TDHolmes/BinaryClock/firmware/LED_drvr_STP16CPC26.c

#include "LED_drvr_STP16CPC26.h"
#include "LED.h"
#include "ports.h"
#include <stdint.h>

/*! \file LED_drvr_STP16CPC26.c
    \brief Low level LED driver functions to be used with the STP16CPC26 LED
    constant current driver.
*/

#define COLOR_DEPTH 4  //!< Number of bits of color to multiplex.


/*!
 * Initializes the LED driver structure and drives the anode port high to
 * avoid LEDs turning on.
 *
 * @param[in] LED_ptr (LED_drvr_t *): pointer to the LED driver structure.
 */
void LED_drvr_init(LED_drvr_t * LED_ptr)
{
    LED_ptr->active_column = 0;
    LED_ptr->active_color_bit = 0;
    ANO_PORT = 0xFF;
}


/*!
 * Runs the LED multiplexing code. Generates a bitstream to send to the LED
 * driver, then activates the corresponding column.
 *
 * @param[in] LED_ptr (LED_drvr_t *): pointer to the LED driver structure.
 */
void LED_drvr_run(LED_drvr_t *LED_ptr)
{
    uint16_t color_mask = (1 << LED_ptr->active_color_bit);
    uint16_t bitstream = 0;
    uint16_t bit = 0;
    uint8_t row;
    uint8_t i;

    // build up the bitstream to be clocked out
    for (row = 0; row < 4; row++) { // rows
        /*  --  RED  --   */
         // mask for color
        bit = (LED_ptr->LED_array[row][LED_ptr->active_column][RED_IND] & color_mask) >> LED_ptr->active_color_bit;
        // shift for bitstream placement and compensate for selected color bi >> LED_ptr->active_color_bitt
        bitstream |= (bit << ((3 - row) * 3 + RED_IND));
        /*  --  GREEN  --   */
        bit = (LED_ptr->LED_array[row][LED_ptr->active_column][GREEN_IND] & color_mask) >> LED_ptr->active_color_bit;
        bitstream |= (bit << ((3 - row) * 3 + GREEN_IND));
        /*  --  BLUE  --   */
        bit = (LED_ptr->LED_array[row][LED_ptr->active_column][BLUE_IND] & color_mask) >> LED_ptr->active_color_bit;
        bitstream |= (bit << ((3 - row) * 3 + BLUE_IND));
    }

    // clock out the LED bits
    for(i = 0; i < 12; i++) {
        LEDDRV_CLK_SET(0);
        LEDDRV_SDI_SET((bitstream >> i) & 0x0001);
        LEDDRV_CLK_SET(1);
    }

    // Turn off LED until everything is set (OE is active low)
    LEDDRV_OE_SET(1);
    // Latch the LED driver data
    LEDDRV_LE_SET(1);
    LEDDRV_LE_SET(0);
    // disable the previous anode
    if (LED_ptr->active_column == 0) {
        ANO_PORT |= (1 << 6);
    } else {
        ANO_PORT |= (1 << (LED_ptr->active_column - 1));
    }
    // Enable the current anode high side
    // the 6th column isn't sequential like the other 5
    if (LED_ptr->active_column != 5) {
        ANO_PORT &= ~(1 << LED_ptr->active_column);
    } else {
        ANO_PORT &= ~(1 << (LED_ptr->active_column + 1));
    }
    // output the LED driver data
    LEDDRV_OE_SET(0);

    // increment the variables in the LED_ptr struct
    if (LED_ptr->active_column < 5) {
        LED_ptr->active_column += 1;
    } else {
        LED_ptr->active_column = 0;
        // update the color bit too
        if (LED_ptr->active_color_bit < COLOR_DEPTH) {
            LED_ptr->active_color_bit += 1;
        } else {
            LED_ptr->active_color_bit = 0;
        }
    }
}
