TDHolmes/BinaryClock/firmware/i2c_drvr_4313.h

#ifndef I2C_DRVR_4313_H__
#define I2C_DRVR_4313_H__

#include "global_defines.h"
#include <stdint.h>

/*! \file i2c_drvr_4313.h
    \brief Low level I2C definitions for the ATtiny4313.
*/

#define I2C_START_RETRY 5 //!< defines how many times we should retry to start communication

#define I2C_BITBANG  //!< Don't use I2C hardware modules, but rather manual port manipulation

// function definitions
retval_t i2c_drvr_init(void);
retval_t i2c_drvr_start(uint8_t byte_to_tx);
retval_t i2c_drvr_end(void);
retval_t i2c_drvr_write_byte(uint8_t byte_to_tx);
    retval_t i2c_drvr_read_byte(uint8_t *byte_read_ptr, uint8_t ack);

void toggle_scl(void);

#endif /* I2C_DRVR_4313_H__ */
